energietransitie/twomes-opentherm-monitor-hardware/images/twomes-opentherm-monitor-hardware-v1.0-bottom.png

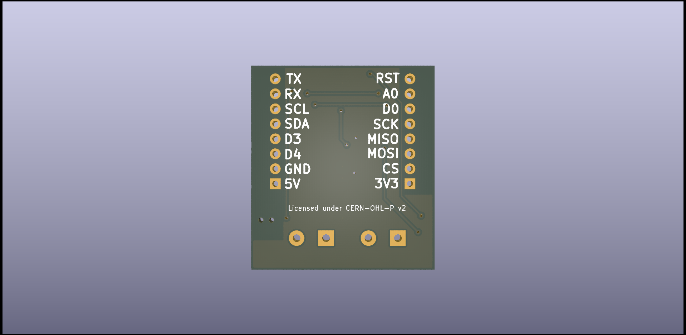
images/twomes-opentherm-monitor-hardware-v1.0-bottom.png
